an-ven/graspib/GrasPiB_AR488_Adapter/Documentation/GrasPiB_AR488_Adapter-F_SilkS.pdf

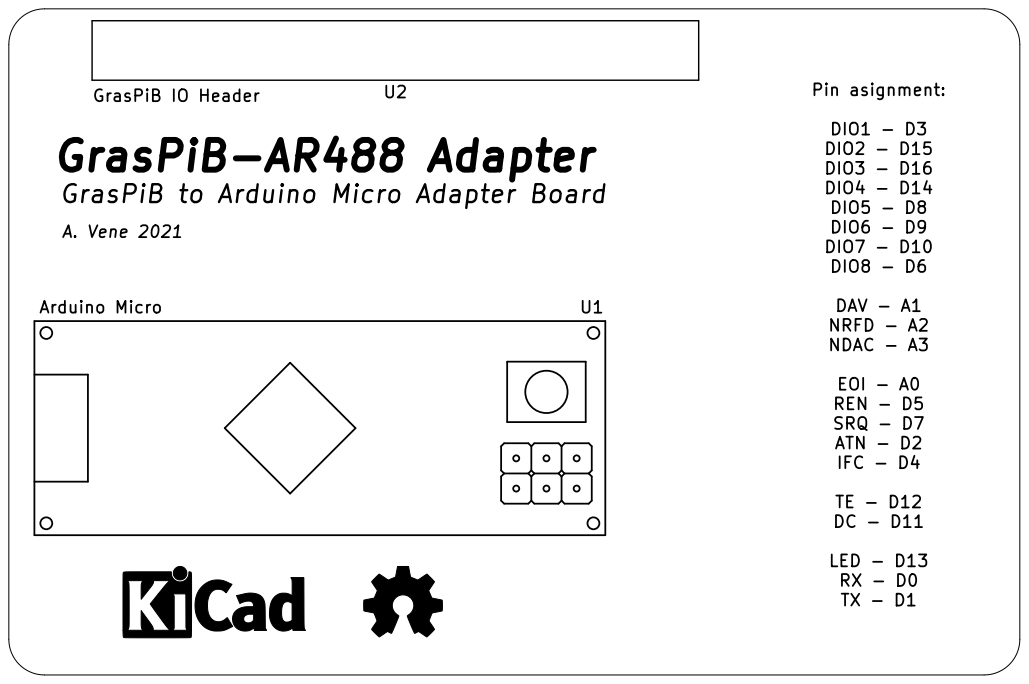
[picture p15: page 1]

IFC - D4 TE - D12 DC - D11 LED - D13 RX - D0 TX - D1 GrasPiB to Arduino Micro Adapter Board

File: GrasPiB_AR488_Adapter.kicad_pcb Sheet: A. Vene GrasPiB to Arduino Micro Adapter Board

Id: 1/1 Title: GrasPiB-AR488 Adapter
